acp-bionano/eppenTemp.Jason/test/tests 08:02/freezer/test1.png

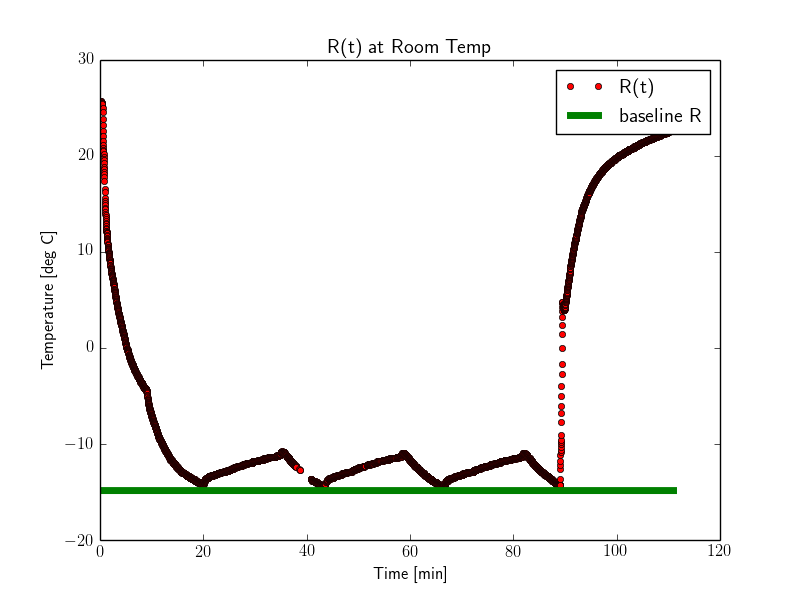
test/tests 08:02/freezer/test1.png
