acp-bionano/eppenTemp.Jason/test/tests 08:02/room temp with sleep/rt1.png

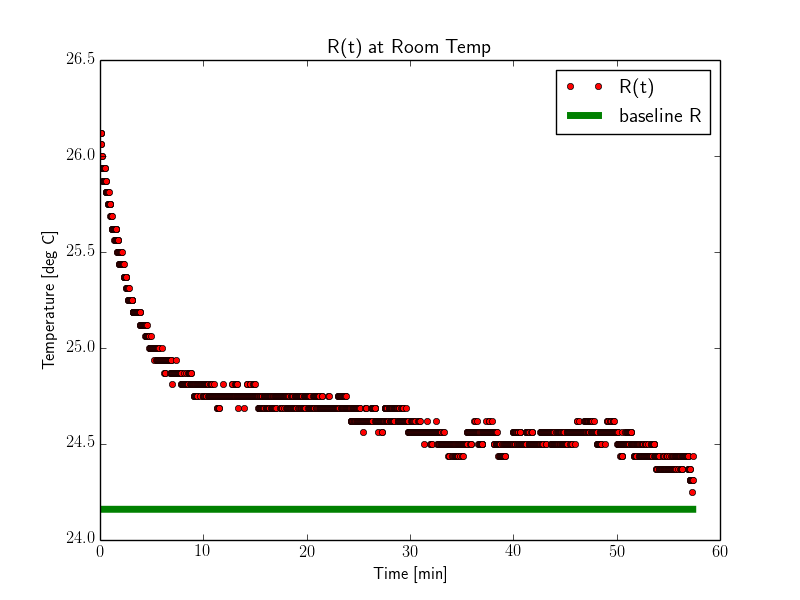
test/tests 08:02/room temp with sleep/rt1.png
